uChip/UGSpi-Touch-Display/EVICIV-7-in-Display/DisplaySide.jpg

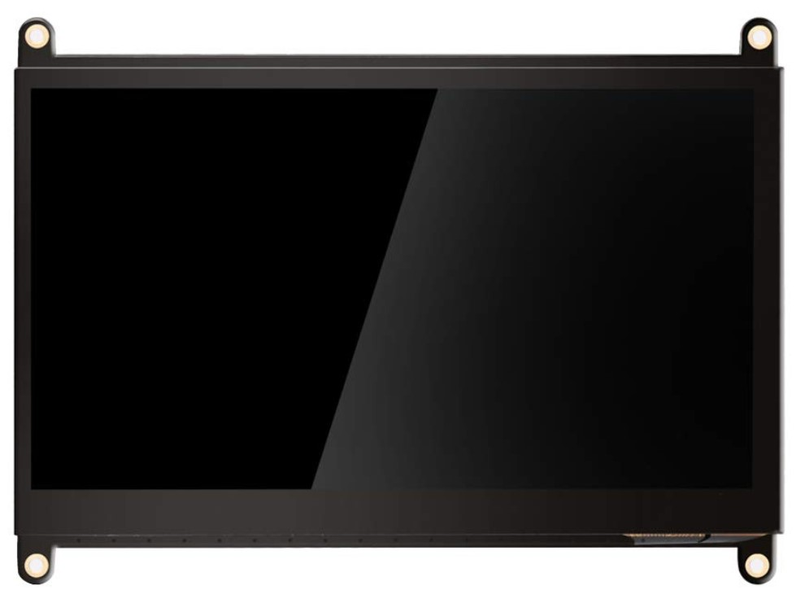
EVICIV-7-in-Display/DisplaySide.jpg
