uChip/UGSpi-Touch-Display/EVICIV-7-in-Display/IMG_0693.jpg

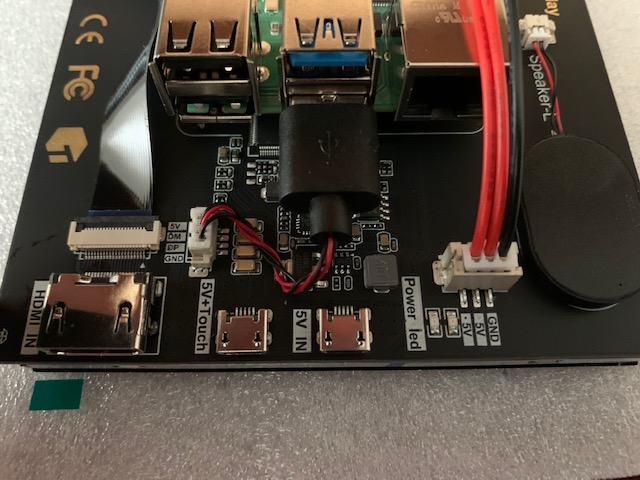
EVICIV-7-in-Display/IMG_0693.jpg
